axelo/bleh/kicad/bleh/bleh.kicad_sch

## KiCad design kicad/bleh/bleh.kicad_sch (2022-11-29)

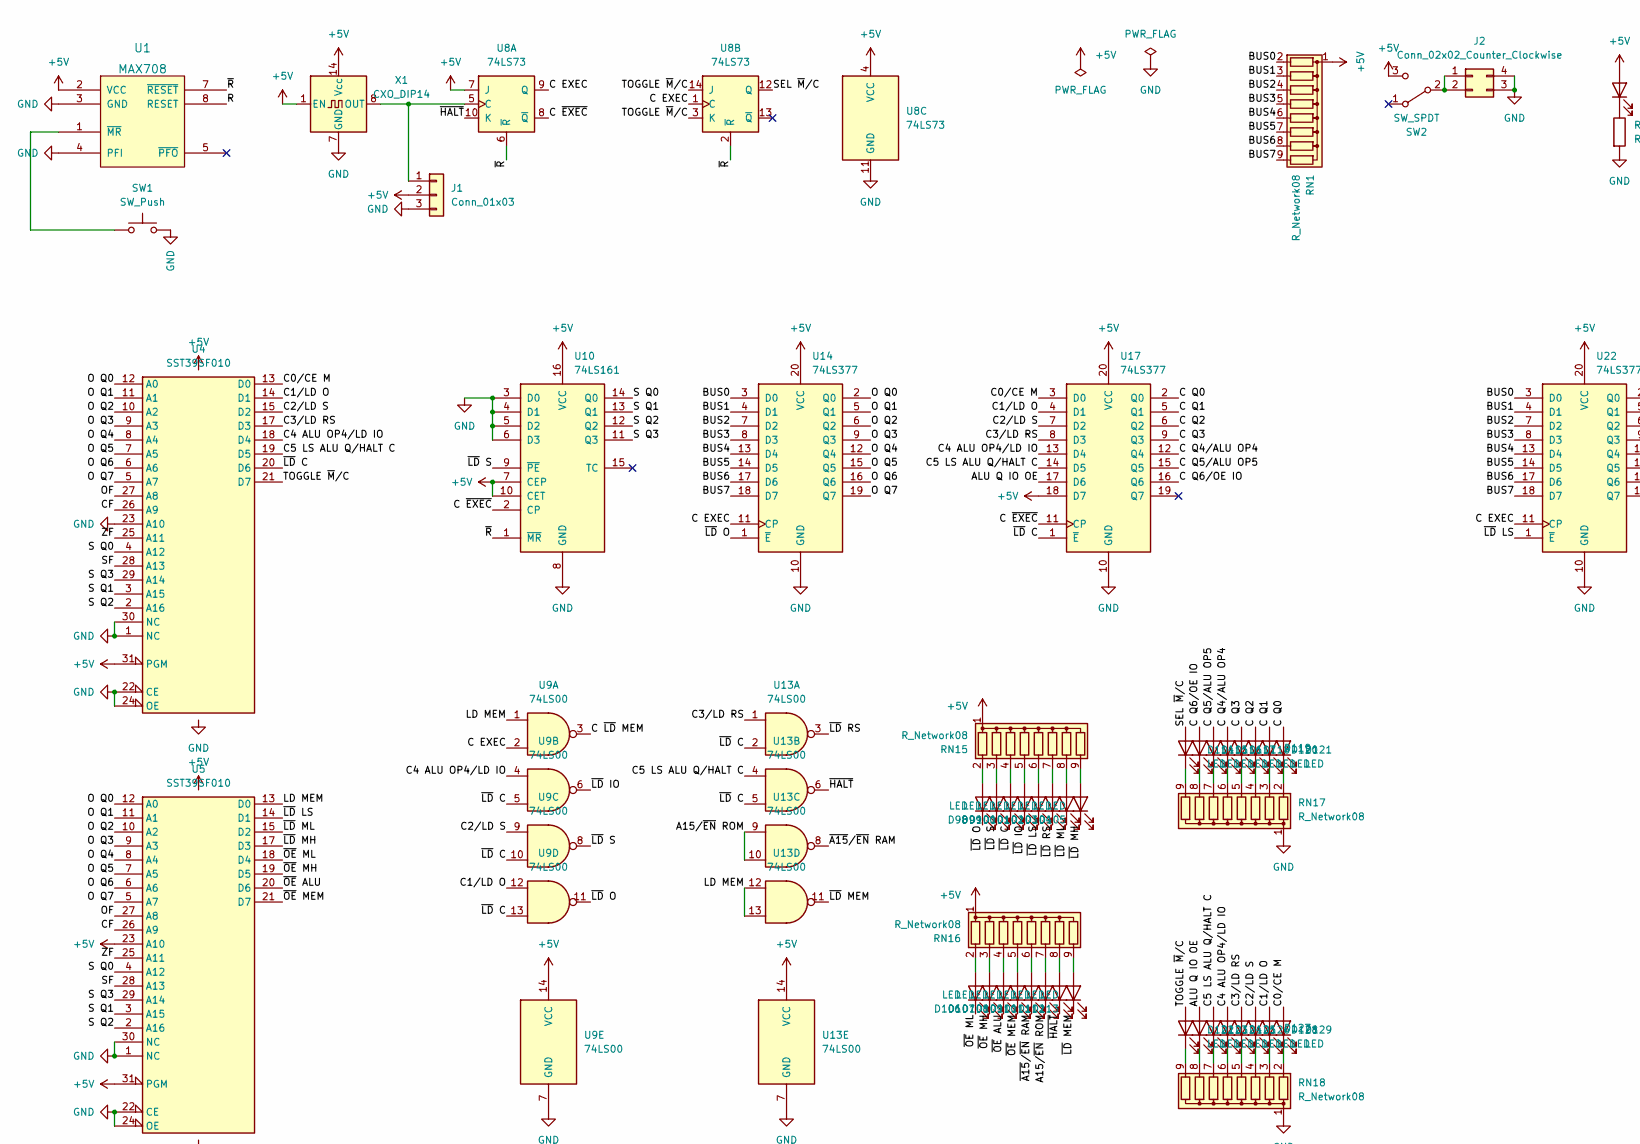
[picture p2: schematic bleh.kicad_sch, part in row 1, column 1]

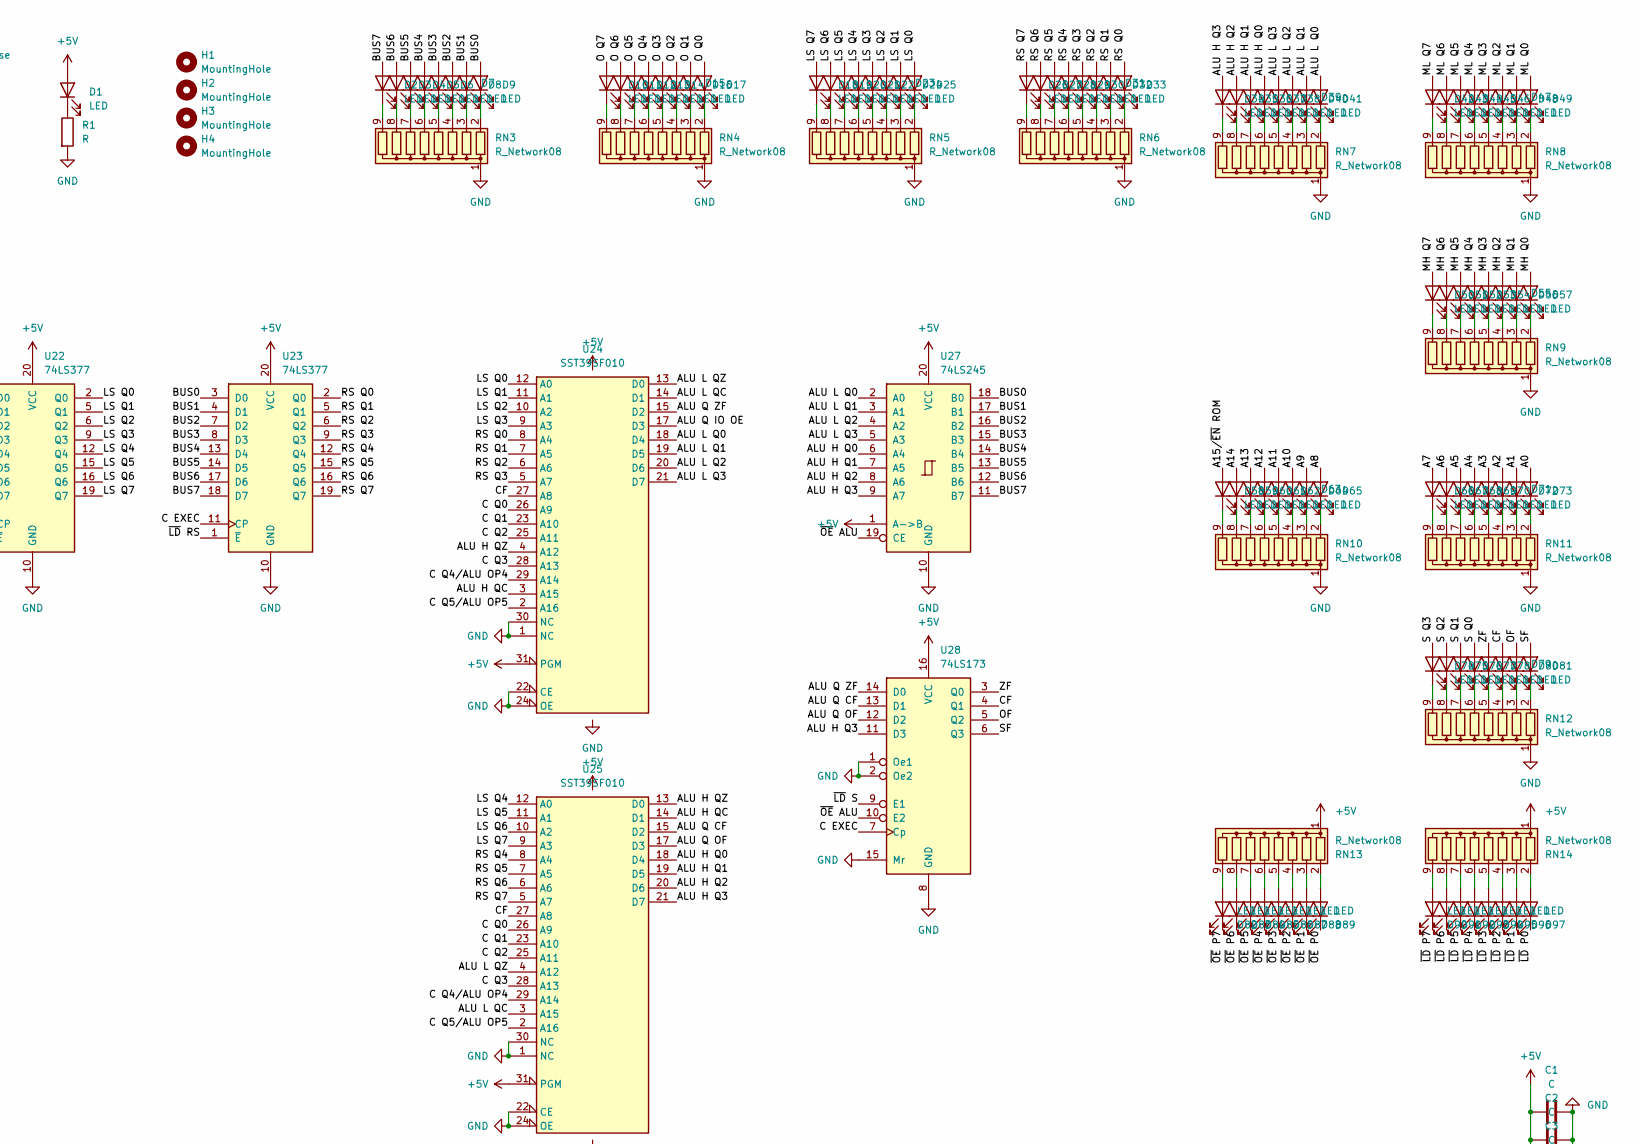
[picture p3: schematic bleh.kicad_sch, part in row 1, column 2]

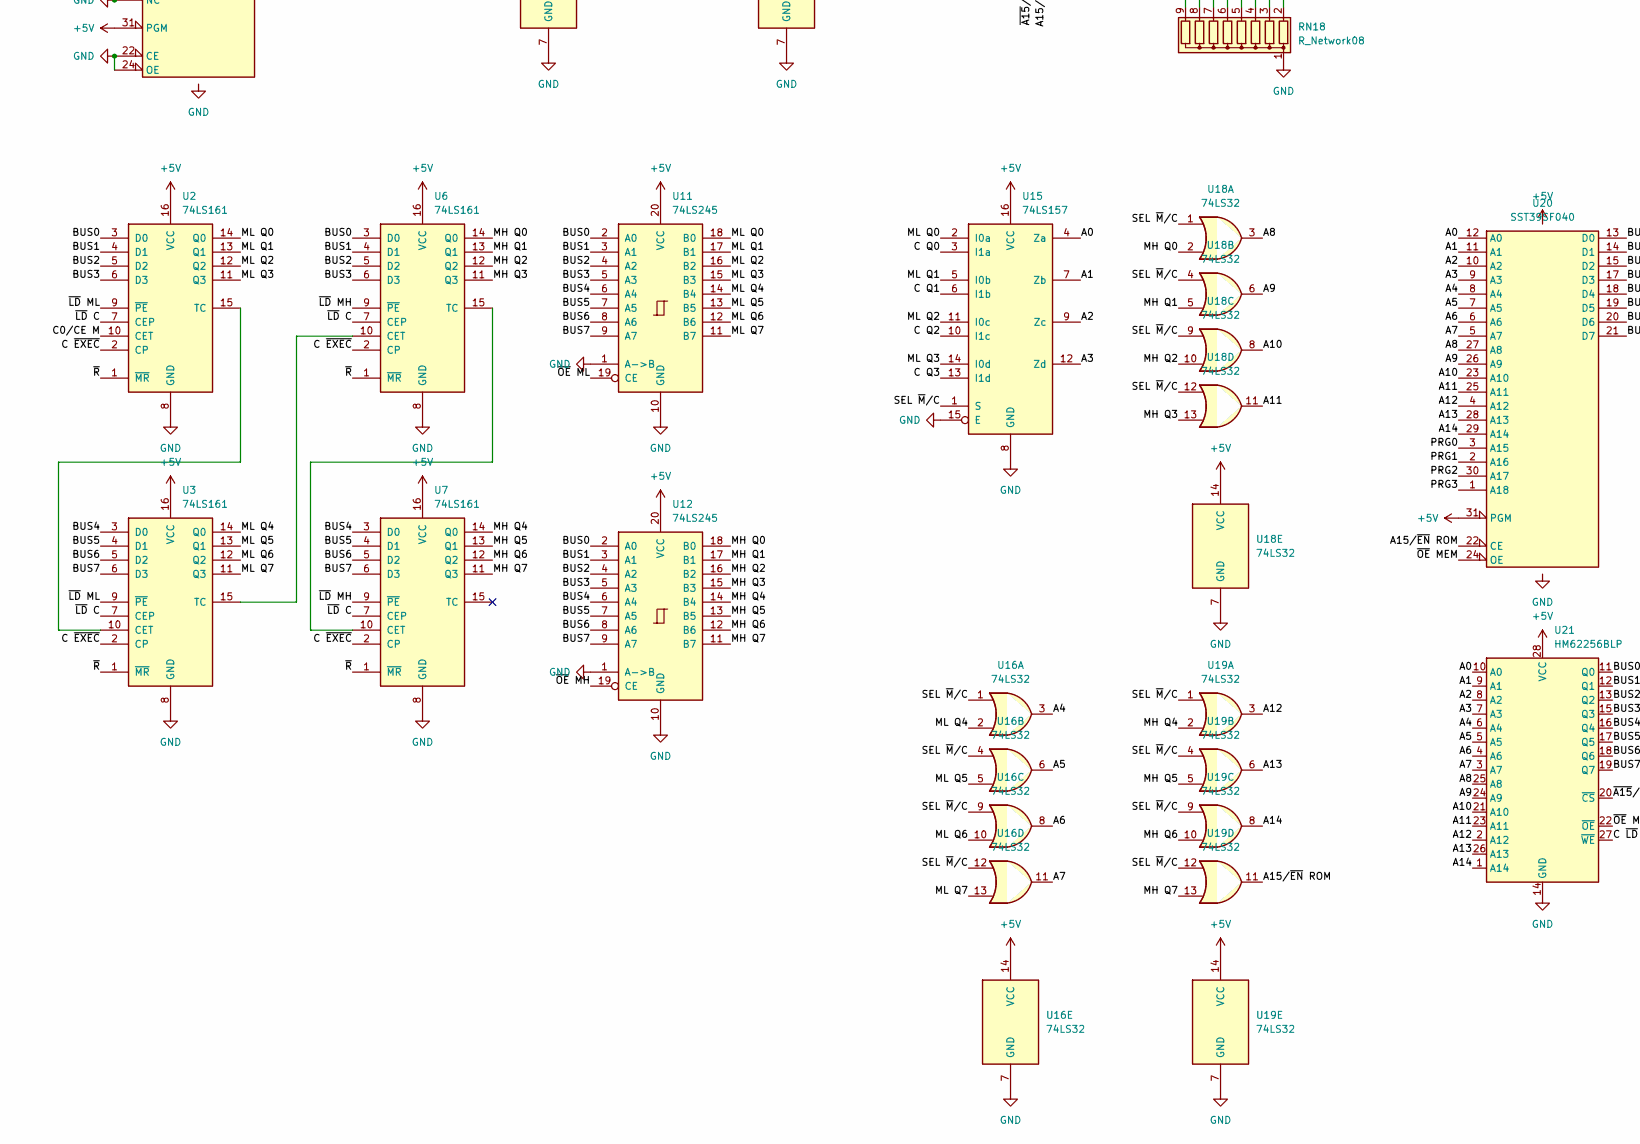
[picture p4: schematic bleh.kicad_sch, part in row 2, column 1]

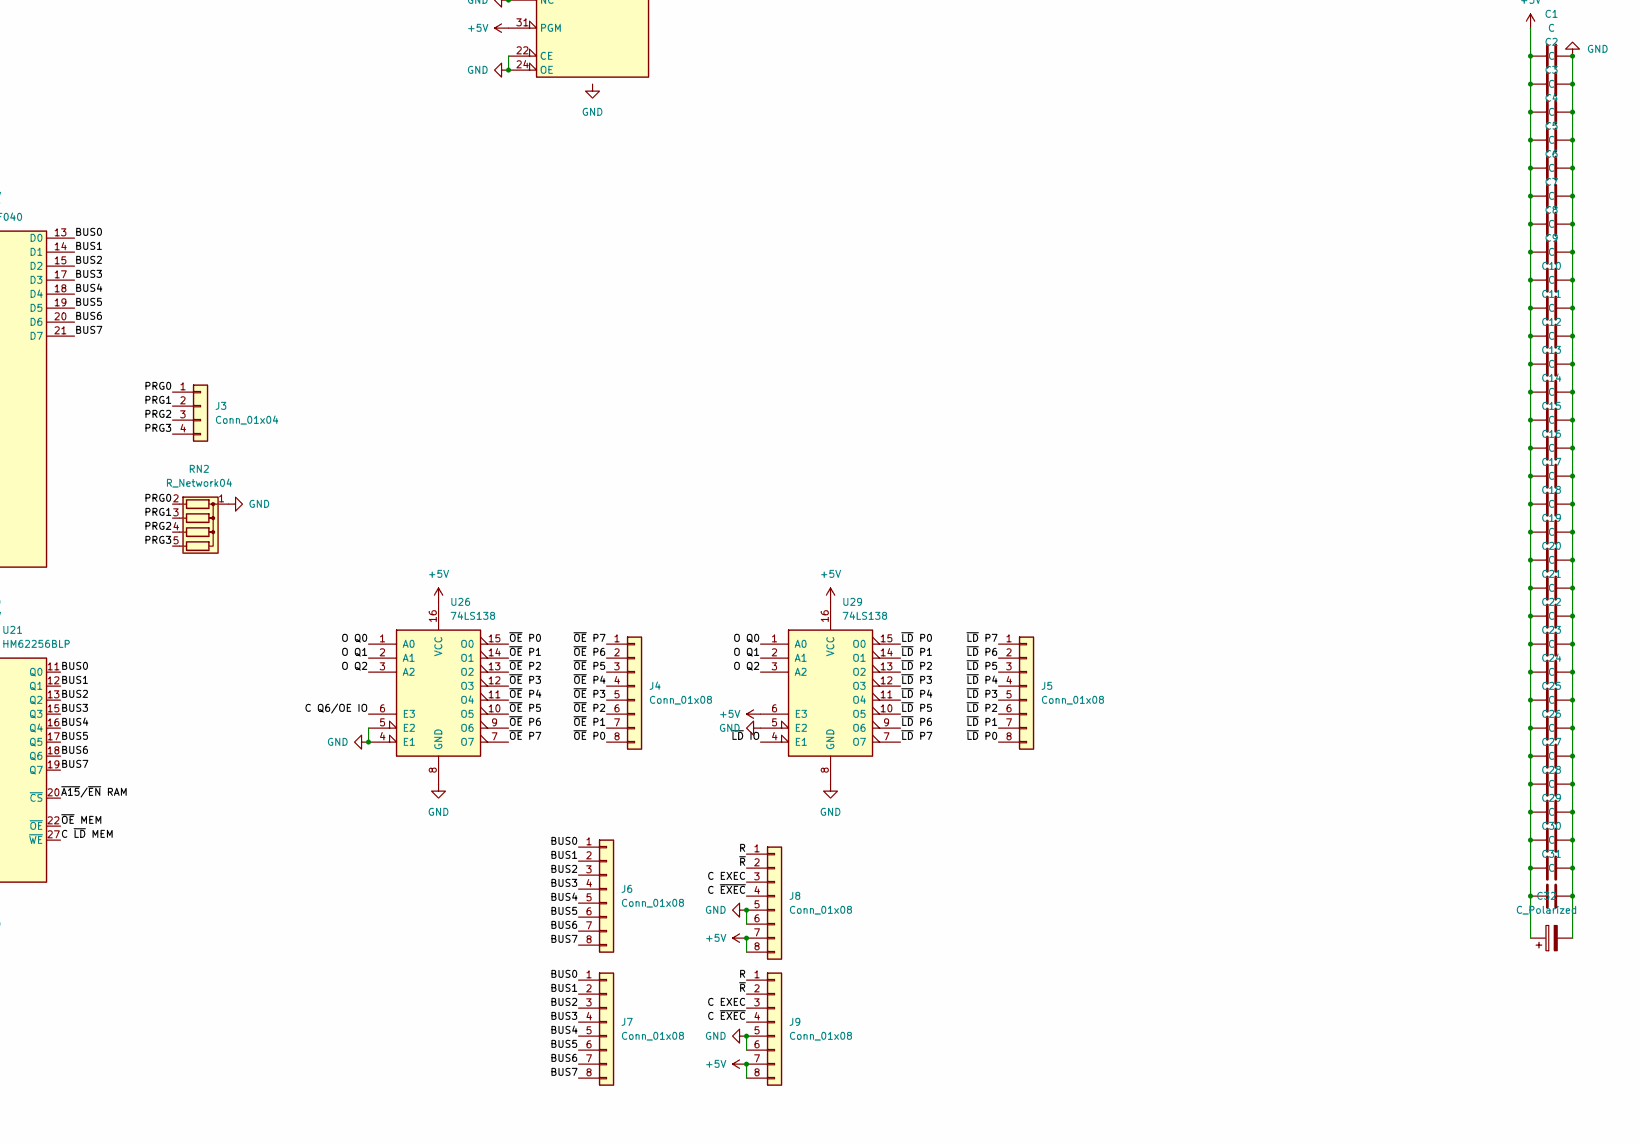
[picture p5: schematic bleh.kicad_sch, part in row 2, column 2]

Parts:
C1, C2, C3, C4, C5, C6, C7, C8, C9, C10, C11, C12, C13, C14, C15, C16, C17, C18, C19, C20, C21, C22, C23, C24, C25, C26, C27, C28, C29, C30, C31: C; C_Disc_D5.0mm_W2.5mm_P2.50mm
C32: C_Polarized; CP_Radial_D6.3mm_P2.50mm
D1, D2, D3, D4, D5, D6, D7, D8, D9, D10, D11, D12, D13, D14, D15, D16, D17, D18, D19, D20, D21, D22, D23, D24, D25, D26, D27, D28, D29, D30, D31, D32, D33, D34, D35, D36, D37, D38, D39, D40, D41, D42, D43, D44, D45, D46, D47, D48, D49, D50, D51, D52, D53, D54, D55, D56, D57, D58, D59, D60, D61, D62, D63, D64, D65, D66, D67, D68, D69, D70, D71, D72, D73, D74, D75, D76, D77, D78, D79, D80, D81, D82, D83, D84, D85, D86, D87, D88, D89, D90, D91, D92, D93, D94, D95, D96, D97, D98, D99, D100, D101, D102, D103, D104, D105, D106, D107, D108, D109, D110, D111, D112, D113, D114, D115, D116, D117, D118, D119, D120, D121, D122, D123, D124, D125, D126, D127, D128, D129: LED; LED_D3.0mm
H1, H2, H3, H4: MountingHole; MountingHole_3.2mm_M3
J1: Conn_01x03; PinSocket_1x03_P2.54mm_Vertical
J2: Conn_02x02_Counter_Clockwise; PinSocket_2x02_P2.54mm_Vertical
J3: Conn_01x04; PinSocket_1x04_P2.54mm_Vertical
J4, J5, J6, J7, J8, J9: Conn_01x08; PinSocket_1x08_P2.54mm_Vertical
R1: R; R_Axial_DIN0204_L3.6mm_D1.6mm_P7.62mm_Horizontal
RN1, RN3, RN4, RN5, RN6, RN7, RN8, RN9, RN10, RN11, RN12, RN13, RN14, RN15, RN16, RN17, RN18: R_Network08; R_Array_SIP9
RN2: R_Network04; R_Array_SIP5
SW1: SW_Push; SW_PUSH_6mm
SW2: SW_SPDT; PinHeader_1x03_P2.54mm_Vertical
U1: MAX708; DIP-8_W7.62mm_Socket
U2, U3, U6, U7, U10: 74LS161; DIP-16_W7.62mm_Socket
U4, U5, U24, U25: SST39SF010; DIP-32_W15.24mm_Socket
U8: 74LS73; DIP-14_W7.62mm_Socket
U9, U13: 74LS00; DIP-14_W7.62mm_Socket
U11, U12, U27: 74LS245; DIP-20_W7.62mm_Socket
U14, U17, U22, U23: 74LS377; DIP-20_W7.62mm_Socket
U15: 74LS157; DIP-16_W7.62mm_Socket
U16, U18, U19: 74LS32; DIP-14_W7.62mm_Socket
U20: SST39SF040; DIP-32_W15.24mm_Socket
U21: HM62256BLP; DIP-28_W15.24mm_Socket
U26, U29: 74LS138; DIP-16_W7.62mm_Socket
U28: 74LS173; DIP-16_W7.62mm_Socket
X1: CXO_DIP14; Oscillator_DIP-14

Connections:
+5V: C1.1, C2.1, C3.1, C4.1, C5.1, C6.1, C7.1, C8.1, C9.1, C10.1, C11.1, C12.1, C13.1, C14.1, C15.1, C16.1, C17.1, C18.1, C19.1, C20.1, C21.1, C22.1, C23.1, C24.1, C25.1, C26.1, C27.1, C28.1, C29.1, C30.1, C31.1, C32.1, D1.2 (A), J1.2, J8.7, J8.8, J9.7, J9.8, RN1.1 (common), RN13.1 (common), RN14.1 (common), RN15.1 (common), RN16.1 (common), SW2.3 (C), U1.2 (VCC), U2.16 (VCC), U3.16 (VCC), U4.31 (PGM), U4.32 (VCC), U5.23 (A10), U5.31 (PGM), U5.32 (VCC), U6.16 (VCC), U7.16 (VCC), U8.4 (VCC), U8.7 (J), U9.14 (VCC), U10.7 (CEP), U10.10 (CET), U10.16 (VCC), U11.20 (VCC), U12.20 (VCC), U13.14 (VCC), U14.20 (VCC), U15.16 (VCC), U16.14 (VCC), U17.18 (D7), U17.20 (VCC), U18.14 (VCC), U19.14 (VCC), U20.31 (PGM), U20.32 (VCC), U21.28 (VCC), U22.20 (VCC), U23.20 (VCC), U24.31 (PGM), U24.32 (VCC), U25.31 (PGM), U25.32 (VCC), U26.16 (VCC), U27.1 (A->B), U27.20 (VCC), U28.16 (VCC), U29.6 (E3), U29.16 (VCC), X1.1 (EN), X1.14 (Vcc)
A0: D73.2 (A), U15.4 (Za), U20.12 (A0), U21.10 (A0)
A1: D72.2 (A), U15.7 (Zb), U20.11 (A1), U21.9 (A1)
A2: D71.2 (A), U15.9 (Zc), U20.10 (A2), U21.8 (A2)
A3: D70.2 (A), U15.12 (Zd), U20.9 (A3), U21.7 (A3)
A4: D69.2 (A), U16.3, U20.8 (A4), U21.6 (A4)
A5: D68.2 (A), U16.6, U20.7 (A5), U21.5 (A5)
A6: D67.2 (A), U16.8, U20.6 (A6), U21.4 (A6)
A7: D66.2 (A), U16.11, U20.5 (A7), U21.3 (A7)
A8: D65.2 (A), U18.3, U20.27 (A8), U21.25 (A8)
A9: D64.2 (A), U18.6, U20.26 (A9), U21.24 (A9)
A10: D63.2 (A), U18.8, U20.23 (A10), U21.21 (A10)
A11: D62.2 (A), U18.11, U20.25 (A11), U21.23 (A11)
A12: D61.2 (A), U19.3, U20.4 (A12), U21.2 (A12)
A13: D60.2 (A), U19.6, U20.28 (A13), U21.26 (A13)
A14: D59.2 (A), U19.8, U20.29 (A14), U21.1 (A14)
A15/~EN ROM: D58.2 (A), D111.1 (K), U13.9, U13.10, U19.11, U20.22 (CE)
ALU H Q0: D37.2 (A), U25.18 (D4), U27.6 (A4)
ALU H Q1: D36.2 (A), U25.19 (D5), U27.7 (A5)
ALU H Q2: D35.2 (A), U25.20 (D6), U27.8 (A6)
ALU H Q3: D34.2 (A), U25.21 (D7), U27.9 (A7), U28.11 (D3)
ALU H QC: U24.3 (A15), U25.14 (D1)
ALU H QZ: U24.4 (A12), U25.13 (D0)
ALU L Q0: D41.2 (A), U24.18 (D4), U27.2 (A0)
ALU L Q1: D40.2 (A), U24.19 (D5), U27.3 (A1)
ALU L Q2: D39.2 (A), U24.20 (D6), U27.4 (A2)
ALU L Q3: D38.2 (A), U24.21 (D7), U27.5 (A3)
ALU L QC: U24.14 (D1), U25.3 (A15)
ALU L QZ: U24.13 (D0), U25.4 (A12)
ALU Q CF: U25.15 (D2), U28.13 (D1)
ALU Q IO OE: D123.2 (A), U17.17 (D6), U24.17 (D3)
ALU Q OF: U25.17 (D3), U28.12 (D2)
ALU Q ZF: U24.15 (D2), U28.14 (D0)
BUS0: D9.2 (A), J6.1, J7.1, RN1.2 (R1), U2.3 (D0), U6.3 (D0), U11.2 (A0), U12.2 (A0), U14.3 (D0), U20.13 (D0), U21.11 (Q0), U22.3 (D0), U23.3 (D0), U27.18 (B0)
BUS1: D8.2 (A), J6.2, J7.2, RN1.3 (R2), U2.4 (D1), U6.4 (D1), U11.3 (A1), U12.3 (A1), U14.4 (D1), U20.14 (D1), U21.12 (Q1), U22.4 (D1), U23.4 (D1), U27.17 (B1)
BUS2: D7.2 (A), J6.3, J7.3, RN1.4 (R3), U2.5 (D2), U6.5 (D2), U11.4 (A2), U12.4 (A2), U14.7 (D2), U20.15 (D2), U21.13 (Q2), U22.7 (D2), U23.7 (D2), U27.16 (B2)
BUS3: D6.2 (A), J6.4, J7.4, RN1.5 (R4), U2.6 (D3), U6.6 (D3), U11.5 (A3), U12.5 (A3), U14.8 (D3), U20.17 (D3), U21.15 (Q3), U22.8 (D3), U23.8 (D3), U27.15 (B3)
BUS4: D5.2 (A), J6.5, J7.5, RN1.6 (R5), U3.3 (D0), U7.3 (D0), U11.6 (A4), U12.6 (A4), U14.13 (D4), U20.18 (D4), U21.16 (Q4), U22.13 (D4), U23.13 (D4), U27.14 (B4)
BUS5: D4.2 (A), J6.6, J7.6, RN1.7 (R6), U3.4 (D1), U7.4 (D1), U11.7 (A5), U12.7 (A5), U14.14 (D5), U20.19 (D5), U21.17 (Q5), U22.14 (D5), U23.14 (D5), U27.13 (B5)
BUS6: D3.2 (A), J6.7, J7.7, RN1.8 (R7), U3.5 (D2), U7.5 (D2), U11.8 (A6), U12.8 (A6), U14.17 (D6), U20.20 (D6), U21.18 (Q6), U22.17 (D6), U23.17 (D6), U27.12 (B6)
BUS7: D2.2 (A), J6.8, J7.8, RN1.9 (R8), U3.6 (D3), U7.6 (D3), U11.9 (A7), U12.9 (A7), U14.18 (D7), U20.21 (D7), U21.19 (Q7), U22.18 (D7), U23.18 (D7), U27.11 (B7)
C0/CE M: D129.2 (A), U2.10 (CET), U4.13 (D0), U17.3 (D0)
C1/LD O: D128.2 (A), U4.14 (D1), U9.12, U17.4 (D1)
C2/LD S: D127.2 (A), U4.15 (D2), U9.9, U17.7 (D2)
C3/LD RS: D126.2 (A), U4.17 (D3), U13.1, U17.8 (D3)
C4 ALU OP4/LD IO: D125.2 (A), U4.18 (D4), U9.4, U17.13 (D4)
C5 LS ALU Q/HALT C: D124.2 (A), U4.19 (D5), U13.4, U17.14 (D5)
C EXEC: J8.3, J9.3, U8.1 (C), U8.9 (Q), U9.2, U14.11 (CP), U22.11 (CP), U23.11 (CP), U28.7 (Cp)
C Q0: D121.2 (A), U15.3 (I1a), U17.2 (Q0), U24.26 (A9), U25.26 (A9)
C Q1: D120.2 (A), U15.6 (I1b), U17.5 (Q1), U24.23 (A10), U25.23 (A10)
C Q2: D119.2 (A), U15.10 (I1c), U17.6 (Q2), U24.25 (A11), U25.25 (A11)
C Q3: D118.2 (A), U15.13 (I1d), U17.9 (Q3), U24.28 (A13), U25.28 (A13)
C Q4/ALU OP4: D117.2 (A), U17.12 (Q4), U24.29 (A14), U25.29 (A14)
C Q5/ALU OP5: D116.2 (A), U17.15 (Q5), U24.2 (A16), U25.2 (A16)
C Q6/OE IO: D115.2 (A), U17.16 (Q6), U26.6 (E3)
C ~EXEC: J8.4, J9.4, U2.2 (CP), U3.2 (CP), U6.2 (CP), U7.2 (CP), U8.8 (~Q), U10.2 (CP), U17.11 (CP)
C ~LD MEM: U9.3, U21.27 (~WE)
CF: D79.2 (A), U4.26 (A9), U5.26 (A9), U24.27 (A8), U25.27 (A8), U28.4 (Q1)
GND: C1.2, C2.2, C3.2, C4.2, C5.2, C6.2, C7.2, C8.2, C9.2, C10.2, C11.2, C12.2, C13.2, C14.2, C15.2, C16.2, C17.2, C18.2, C19.2, C20.2, C21.2, C22.2, C23.2, C24.2, C25.2, C26.2, C27.2, C28.2, C29.2, C30.2, C31.2, C32.2, J1.3, J2.3, J2.4, J8.5, J8.6, J9.5, J9.6, R1.2, RN2.1 (common), RN3.1 (common), RN4.1 (common), RN5.1 (common), RN6.1 (common), RN7.1 (common), RN8.1 (common), RN9.1 (common), RN10.1 (common), RN11.1 (common), RN12.1 (common), RN17.1 (common), RN18.1 (common), SW1.2, U1.3 (GND), U1.4 (PFI), U2.8 (GND), U3.8 (GND), U4.1 (NC), U4.16 (GND), U4.22 (CE), U4.23 (A10), U4.24 (OE), U4.30 (NC), U5.1 (NC), U5.16 (GND), U5.22 (CE), U5.24 (OE), U5.30 (NC), U6.8 (GND), U7.8 (GND), U8.11 (GND), U9.7 (GND), U10.3 (D0), U10.4 (D1), U10.5 (D2), U10.6 (D3), U10.8 (GND), U11.1 (A->B), U11.10 (GND), U12.1 (A->B), U12.10 (GND), U13.7 (GND), U14.10 (GND), U15.8 (GND), U15.15 (E), U16.7 (GND), U17.10 (GND), U18.7 (GND), U19.7 (GND), U20.16 (GND), U21.14 (GND), U22.10 (GND), U23.10 (GND), U24.1 (NC), U24.16 (GND), U24.22 (CE), U24.24 (OE), U24.30 (NC), U25.1 (NC), U25.16 (GND), U25.22 (CE), U25.24 (OE), U25.30 (NC), U26.4 (E1), U26.5 (E2), U26.8 (GND), U27.10 (GND), U28.1 (Oe1), U28.2 (Oe2), U28.8 (GND), U28.15 (Mr), U29.5 (E2), U29.8 (GND), X1.7 (GND)
LD MEM: U5.13 (D0), U9.1, U13.12, U13.13
LS Q0: D25.2 (A), U22.2 (Q0), U24.12 (A0)
LS Q1: D24.2 (A), U22.5 (Q1), U24.11 (A1)
LS Q2: D23.2 (A), U22.6 (Q2), U24.10 (A2)
LS Q3: D22.2 (A), U22.9 (Q3), U24.9 (A3)
LS Q4: D21.2 (A), U22.12 (Q4), U25.12 (A0)
LS Q5: D20.2 (A), U22.15 (Q5), U25.11 (A1)
LS Q6: D19.2 (A), U22.16 (Q6), U25.10 (A2)
LS Q7: D18.2 (A), U22.19 (Q7), U25.9 (A3)
MH Q0: D57.2 (A), U6.14 (Q0), U12.18 (B0), U18.2
MH Q1: D56.2 (A), U6.13 (Q1), U12.17 (B1), U18.5
MH Q2: D55.2 (A), U6.12 (Q2), U12.16 (B2), U18.10
MH Q3: D54.2 (A), U6.11 (Q3), U12.15 (B3), U18.13
MH Q4: D53.2 (A), U7.14 (Q0), U12.14 (B4), U19.2
MH Q5: D52.2 (A), U7.13 (Q1), U12.13 (B5), U19.5
MH Q6: D51.2 (A), U7.12 (Q2), U12.12 (B6), U19.10
MH Q7: D50.2 (A), U7.11 (Q3), U12.11 (B7), U19.13
ML Q0: D49.2 (A), U2.14 (Q0), U11.18 (B0), U15.2 (I0a)
ML Q1: D48.2 (A), U2.13 (Q1), U11.17 (B1), U15.5 (I0b)
ML Q2: D47.2 (A), U2.12 (Q2), U11.16 (B2), U15.11 (I0c)
ML Q3: D46.2 (A), U2.11 (Q3), U11.15 (B3), U15.14 (I0d)
ML Q4: D45.2 (A), U3.14 (Q0), U11.14 (B4), U16.2
ML Q5: D44.2 (A), U3.13 (Q1), U11.13 (B5), U16.5
ML Q6: D43.2 (A), U3.12 (Q2), U11.12 (B6), U16.10
ML Q7: D42.2 (A), U3.11 (Q3), U11.11 (B7), U16.13
unnamed: D1.1 (K), R1.1
unnamed: D2.1 (K), RN3.9 (R8)
unnamed: D3.1 (K), RN3.8 (R7)
unnamed: D4.1 (K), RN3.7 (R6)
unnamed: D5.1 (K), RN3.6 (R5)
unnamed: D6.1 (K), RN3.5 (R4)
unnamed: D7.1 (K), RN3.4 (R3)
unnamed: D8.1 (K), RN3.3 (R2)
unnamed: D9.1 (K), RN3.2 (R1)
unnamed: D10.1 (K), RN4.9 (R8)
unnamed: D11.1 (K), RN4.8 (R7)
unnamed: D12.1 (K), RN4.7 (R6)
unnamed: D13.1 (K), RN4.6 (R5)
unnamed: D14.1 (K), RN4.5 (R4)
unnamed: D15.1 (K), RN4.4 (R3)
unnamed: D16.1 (K), RN4.3 (R2)
unnamed: D17.1 (K), RN4.2 (R1)
unnamed: D18.1 (K), RN5.9 (R8)
unnamed: D19.1 (K), RN5.8 (R7)
unnamed: D20.1 (K), RN5.7 (R6)
unnamed: D21.1 (K), RN5.6 (R5)
unnamed: D22.1 (K), RN5.5 (R4)
unnamed: D23.1 (K), RN5.4 (R3)
unnamed: D24.1 (K), RN5.3 (R2)
unnamed: D25.1 (K), RN5.2 (R1)
unnamed: D26.1 (K), RN6.9 (R8)
unnamed: D27.1 (K), RN6.8 (R7)
unnamed: D28.1 (K), RN6.7 (R6)
unnamed: D29.1 (K), RN6.6 (R5)
unnamed: D30.1 (K), RN6.5 (R4)
unnamed: D31.1 (K), RN6.4 (R3)
unnamed: D32.1 (K), RN6.3 (R2)
unnamed: D33.1 (K), RN6.2 (R1)
unnamed: D34.1 (K), RN7.9 (R8)
unnamed: D35.1 (K), RN7.8 (R7)
unnamed: D36.1 (K), RN7.7 (R6)
unnamed: D37.1 (K), RN7.6 (R5)
unnamed: D38.1 (K), RN7.5 (R4)
unnamed: D39.1 (K), RN7.4 (R3)
unnamed: D40.1 (K), RN7.3 (R2)
unnamed: D41.1 (K), RN7.2 (R1)
unnamed: D42.1 (K), RN8.9 (R8)
unnamed: D43.1 (K), RN8.8 (R7)
unnamed: D44.1 (K), RN8.7 (R6)
unnamed: D45.1 (K), RN8.6 (R5)
unnamed: D46.1 (K), RN8.5 (R4)
unnamed: D47.1 (K), RN8.4 (R3)
unnamed: D48.1 (K), RN8.3 (R2)
unnamed: D49.1 (K), RN8.2 (R1)
unnamed: D50.1 (K), RN9.9 (R8)
unnamed: D51.1 (K), RN9.8 (R7)
unnamed: D52.1 (K), RN9.7 (R6)
unnamed: D53.1 (K), RN9.6 (R5)
unnamed: D54.1 (K), RN9.5 (R4)
unnamed: D55.1 (K), RN9.4 (R3)
unnamed: D56.1 (K), RN9.3 (R2)
unnamed: D57.1 (K), RN9.2 (R1)
unnamed: D58.1 (K), RN10.9 (R8)
unnamed: D59.1 (K), RN10.8 (R7)
unnamed: D60.1 (K), RN10.7 (R6)
unnamed: D61.1 (K), RN10.6 (R5)
unnamed: D62.1 (K), RN10.5 (R4)
unnamed: D63.1 (K), RN10.4 (R3)
unnamed: D64.1 (K), RN10.3 (R2)
unnamed: D65.1 (K), RN10.2 (R1)
unnamed: D66.1 (K), RN11.9 (R8)
unnamed: D67.1 (K), RN11.8 (R7)
unnamed: D68.1 (K), RN11.7 (R6)
unnamed: D69.1 (K), RN11.6 (R5)
unnamed: D70.1 (K), RN11.5 (R4)
unnamed: D71.1 (K), RN11.4 (R3)
unnamed: D72.1 (K), RN11.3 (R2)
unnamed: D73.1 (K), RN11.2 (R1)
unnamed: D74.1 (K), RN12.9 (R8)
unnamed: D75.1 (K), RN12.8 (R7)
unnamed: D76.1 (K), RN12.7 (R6)
unnamed: D77.1 (K), RN12.6 (R5)
unnamed: D78.1 (K), RN12.5 (R4)
unnamed: D79.1 (K), RN12.4 (R3)
unnamed: D80.1 (K), RN12.3 (R2)
unnamed: D81.1 (K), RN12.2 (R1)
unnamed: D82.2 (A), RN13.9 (R8)
unnamed: D83.2 (A), RN13.8 (R7)
unnamed: D84.2 (A), RN13.7 (R6)
unnamed: D85.2 (A), RN13.6 (R5)
unnamed: D86.2 (A), RN13.5 (R4)
unnamed: D87.2 (A), RN13.4 (R3)
unnamed: D88.2 (A), RN13.3 (R2)
unnamed: D89.2 (A), RN13.2 (R1)
unnamed: D90.2 (A), RN14.9 (R8)
unnamed: D91.2 (A), RN14.8 (R7)
unnamed: D92.2 (A), RN14.7 (R6)
unnamed: D93.2 (A), RN14.6 (R5)
unnamed: D94.2 (A), RN14.5 (R4)
unnamed: D95.2 (A), RN14.4 (R3)
unnamed: D96.2 (A), RN14.3 (R2)
unnamed: D97.2 (A), RN14.2 (R1)
unnamed: D98.2 (A), RN15.2 (R1)
unnamed: D99.2 (A), RN15.3 (R2)
unnamed: D100.2 (A), RN15.4 (R3)
unnamed: D101.2 (A), RN15.5 (R4)
unnamed: D102.2 (A), RN15.6 (R5)
unnamed: D103.2 (A), RN15.7 (R6)
unnamed: D104.2 (A), RN15.8 (R7)
unnamed: D105.2 (A), RN15.9 (R8)
unnamed: D106.2 (A), RN16.2 (R1)
unnamed: D107.2 (A), RN16.3 (R2)
unnamed: D108.2 (A), RN16.4 (R3)
unnamed: D109.2 (A), RN16.5 (R4)
unnamed: D110.2 (A), RN16.6 (R5)
unnamed: D111.2 (A), RN16.7 (R6)
unnamed: D112.2 (A), RN16.8 (R7)
unnamed: D113.2 (A), RN16.9 (R8)
unnamed: D114.1 (K), RN17.9 (R8)
unnamed: D115.1 (K), RN17.8 (R7)
unnamed: D116.1 (K), RN17.7 (R6)
unnamed: D117.1 (K), RN17.6 (R5)
unnamed: D118.1 (K), RN17.5 (R4)
unnamed: D119.1 (K), RN17.4 (R3)
unnamed: D120.1 (K), RN17.3 (R2)
unnamed: D121.1 (K), RN17.2 (R1)
unnamed: D122.1 (K), RN18.9 (R8)
unnamed: D123.1 (K), RN18.8 (R7)
unnamed: D124.1 (K), RN18.7 (R6)
unnamed: D125.1 (K), RN18.6 (R5)
unnamed: D126.1 (K), RN18.5 (R4)
unnamed: D127.1 (K), RN18.4 (R3)
unnamed: D128.1 (K), RN18.3 (R2)
unnamed: D129.1 (K), RN18.2 (R1)
unnamed: J1.1, U8.5 (C), X1.8 (OUT)
unnamed: J2.1, J2.2, SW2.2 (B)
unnamed: SW1.1, U1.1 (~MR)
unnamed: U2.15 (TC), U3.10 (CET)
unnamed: U3.15 (TC), U6.10 (CET)
unnamed: U6.15 (TC), U7.10 (CET)
O Q0: D17.2 (A), U4.12 (A0), U5.12 (A0), U14.2 (Q0), U26.1 (A0), U29.1 (A0)
O Q1: D16.2 (A), U4.11 (A1), U5.11 (A1), U14.5 (Q1), U26.2 (A1), U29.2 (A1)
O Q2: D15.2 (A), U4.10 (A2), U5.10 (A2), U14.6 (Q2), U26.3 (A2), U29.3 (A2)
O Q3: D14.2 (A), U4.9 (A3), U5.9 (A3), U14.9 (Q3)
O Q4: D13.2 (A), U4.8 (A4), U5.8 (A4), U14.12 (Q4)
O Q5: D12.2 (A), U4.7 (A5), U5.7 (A5), U14.15 (Q5)
O Q6: D11.2 (A), U4.6 (A6), U5.6 (A6), U14.16 (Q6)
O Q7: D10.2 (A), U4.5 (A7), U5.5 (A7), U14.19 (Q7)
OF: D80.2 (A), U4.27 (A8), U5.27 (A8), U28.5 (Q2)
PRG0: J3.1, RN2.2 (R1), U20.3 (A15)
PRG1: J3.2, RN2.3 (R2), U20.2 (A16)
PRG2: J3.3, RN2.4 (R3), U20.30 (A17)
PRG3: J3.4, RN2.5 (R4), U20.1 (A18)
R: J8.1, J9.1, U1.8 (RESET)
RS Q0: D33.2 (A), U23.2 (Q0), U24.8 (A4)
RS Q1: D32.2 (A), U23.5 (Q1), U24.7 (A5)
RS Q2: D31.2 (A), U23.6 (Q2), U24.6 (A6)
RS Q3: D30.2 (A), U23.9 (Q3), U24.5 (A7)
RS Q4: D29.2 (A), U23.12 (Q4), U25.8 (A4)
RS Q5: D28.2 (A), U23.15 (Q5), U25.7 (A5)
RS Q6: D27.2 (A), U23.16 (Q6), U25.6 (A6)
RS Q7: D26.2 (A), U23.19 (Q7), U25.5 (A7)
S Q0: D77.2 (A), U4.4 (A12), U5.4 (A12), U10.14 (Q0)
S Q1: D76.2 (A), U4.3 (A15), U5.3 (A15), U10.13 (Q1)
S Q2: D75.2 (A), U4.2 (A16), U5.2 (A16), U10.12 (Q2)
S Q3: D74.2 (A), U4.29 (A14), U5.29 (A14), U10.11 (Q3)
SEL ~M/C: D114.2 (A), U8.12 (Q), U15.1 (S), U16.1, U16.4, U16.9, U16.12, U18.1, U18.4, U18.9, U18.12, U19.1, U19.4, U19.9, U19.12
SF: D81.2 (A), U4.28 (A13), U5.28 (A13), U28.6 (Q3)
TOGGLE ~M/C: D122.2 (A), U4.21 (D7), U8.3 (K), U8.14 (J)
ZF: D78.2 (A), U4.25 (A11), U5.25 (A11), U28.3 (Q0)
~A15/~EN RAM: D110.1 (K), U13.8, U21.20 (~CS)
~HALT: D112.1 (K), U8.10 (K), U13.6
~LD C: D100.1 (K), U2.7 (CEP), U3.7 (CEP), U4.20 (D6), U6.7 (CEP), U7.7 (CEP), U9.5, U9.10, U9.13, U13.2, U13.5, U17.1 (~E)
~LD IO: D101.1 (K), U9.6, U29.4 (E1)
~LD LS: D102.1 (K), U5.14 (D1), U22.1 (~E)
~LD MEM: D113.1 (K), U13.11
~LD MH: D105.1 (K), U5.17 (D3), U6.9 (~PE), U7.9 (~PE)
~LD ML: D104.1 (K), U2.9 (~PE), U3.9 (~PE), U5.15 (D2)
~LD O: D98.1 (K), U9.11, U14.1 (~E)
~LD P0: D97.1 (K), J5.8, U29.15 (O0)
~LD P1: D96.1 (K), J5.7, U29.14 (O1)
~LD P2: D95.1 (K), J5.6, U29.13 (O2)
~LD P3: D94.1 (K), J5.5, U29.12 (O3)
~LD P4: D93.1 (K), J5.4, U29.11 (O4)
~LD P5: D92.1 (K), J5.3, U29.10 (O5)
~LD P6: D91.1 (K), J5.2, U29.9 (O6)
~LD P7: D90.1 (K), J5.1, U29.7 (O7)
~LD RS: D103.1 (K), U13.3, U23.1 (~E)
~LD S: D99.1 (K), U9.8, U10.9 (~PE), U28.9 (E1)
~OE ALU: D108.1 (K), U5.20 (D6), U27.19 (CE), U28.10 (E2)
~OE MEM: D109.1 (K), U5.21 (D7), U20.24 (OE), U21.22 (~OE)
~OE MH: D107.1 (K), U5.19 (D5), U12.19 (CE)
~OE ML: D106.1 (K), U5.18 (D4), U11.19 (CE)
~OE P0: D89.1 (K), J4.8, U26.15 (O0)
~OE P1: D88.1 (K), J4.7, U26.14 (O1)
~OE P2: D87.1 (K), J4.6, U26.13 (O2)
~OE P3: D86.1 (K), J4.5, U26.12 (O3)
~OE P4: D85.1 (K), J4.4, U26.11 (O4)
~OE P5: D84.1 (K), J4.3, U26.10 (O5)
~OE P6: D83.1 (K), J4.2, U26.9 (O6)
~OE P7: D82.1 (K), J4.1, U26.7 (O7)
~R: J8.2, J9.2, U1.7 (~RESET), U2.1 (~MR), U3.1 (~MR), U6.1 (~MR), U7.1 (~MR), U8.2 (~R), U8.6 (~R), U10.1 (~MR)
